smaldragon/fennec/src/vars.asm

.cpu 65c02
.var BANK       $4000
.var M_DUMMY    $8000
.var M_A0       $8010
.var M_LCD      $8020
.var M_SD       $8030
.var M_RTC      $8040
.var M_BEEP     $8070
.var M_SYS      $8001
.var ROM        $E000
